Raphael-Boichot/The-TinyGB-Printer/Images/Final_version_2.0_2.png

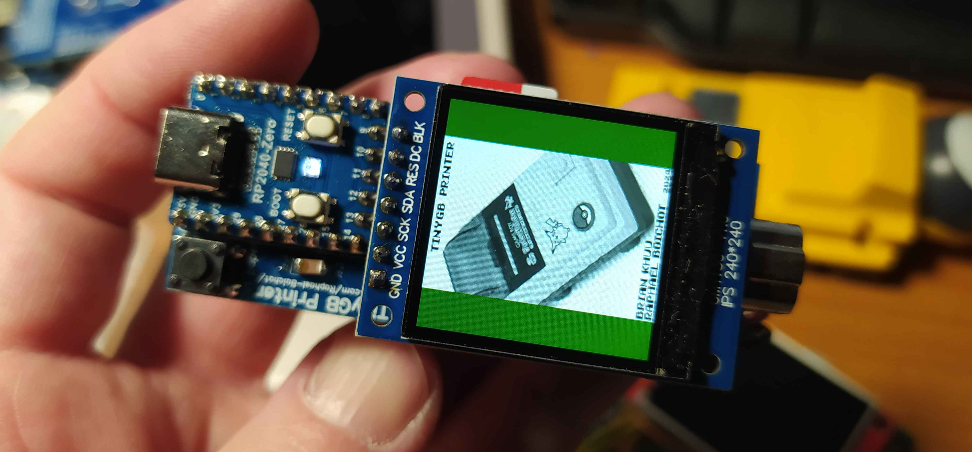
Images/Final_version_2.0_2.png
