Raphael-Boichot/The-TinyGB-Printer/Images/First_prototype.jpg

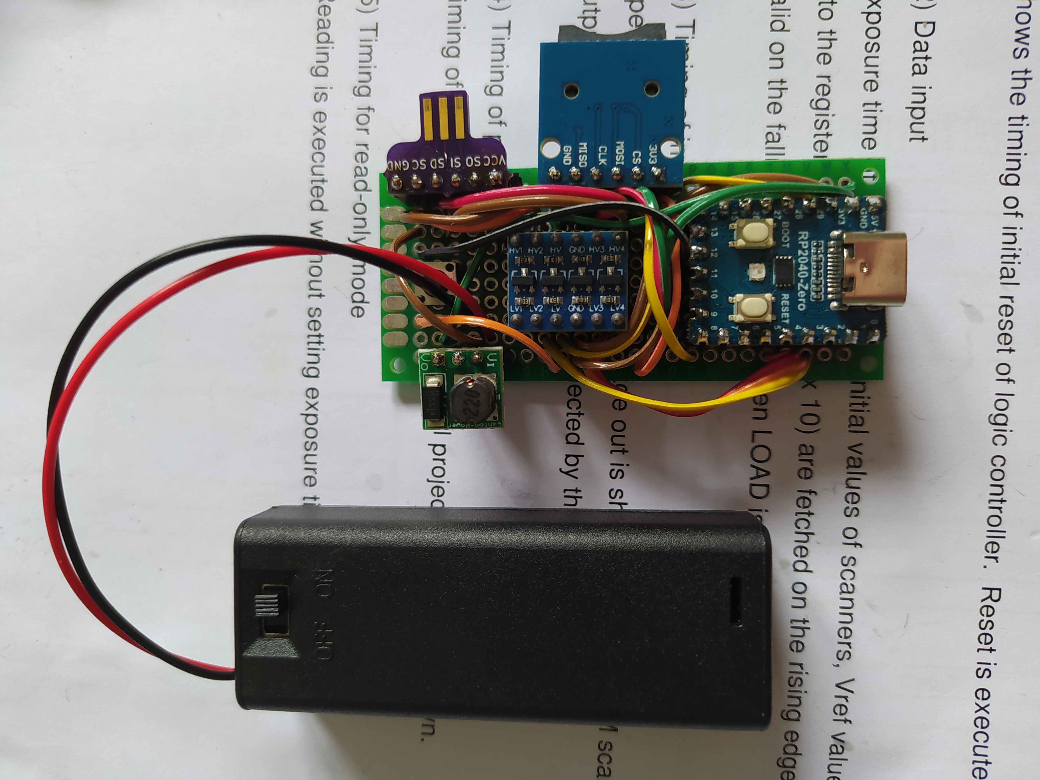
Images/First_prototype.jpg
