Raphael-Boichot/The-TinyGB-Printer/Images/Game_Boy_Camera_2.png

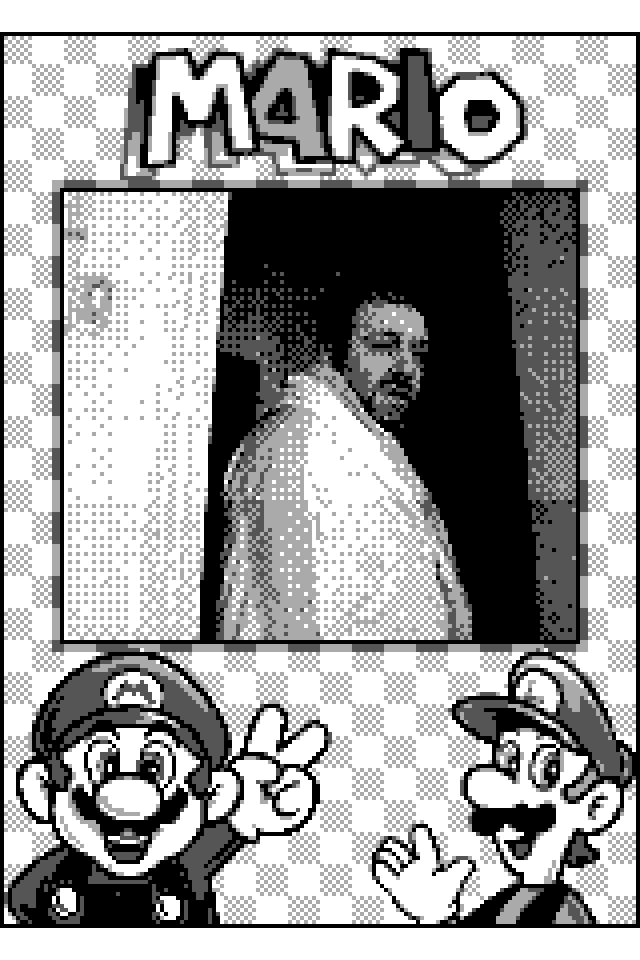
Images/Game_Boy_Camera_2.png
