Raphael-Boichot/The-TinyGB-Printer/Images/Showcase_1.gif

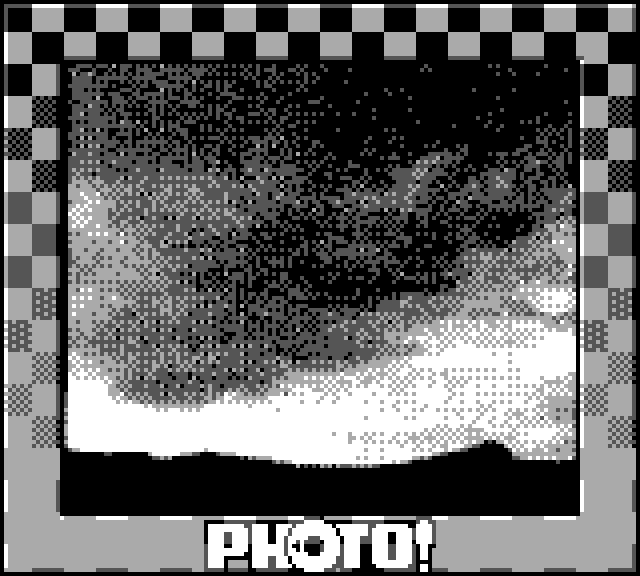
Images/Showcase_1.gif
