Raphael-Boichot/The-TinyGB-Printer/PCB_1.0_without_TFT/PCB.png

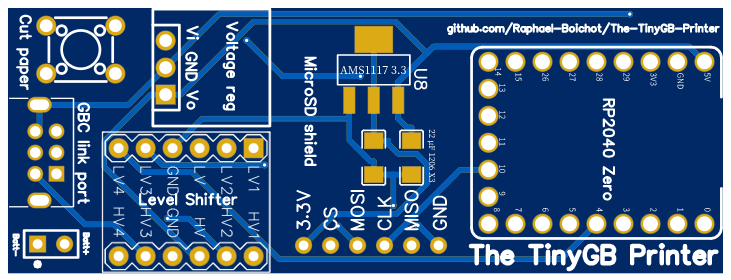
PCB_1.0_without_TFT/PCB.png
