Raphael-Boichot/The-TinyGB-Printer/SD/Script_for_animated_gif/Pictures/0002010.png

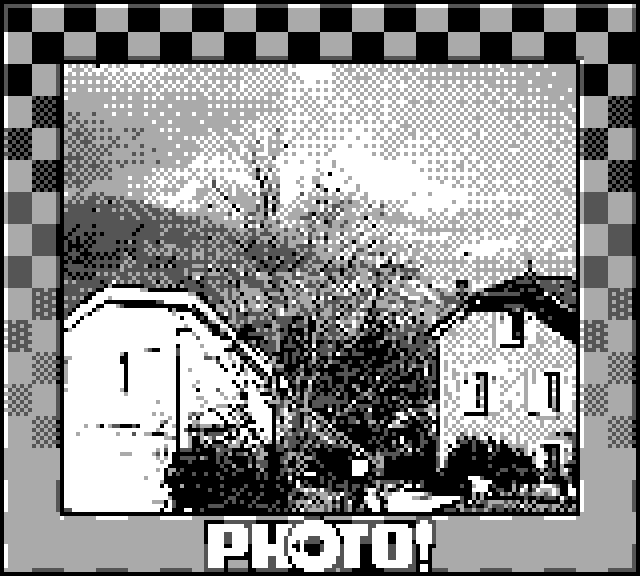
SD/Script_for_animated_gif/Pictures/0002010.png
