Raphael-Boichot/The-TinyGB-Printer/SD/Scripts_for_AEB_mode/Code_black_and_white/Pictures/0004069.png

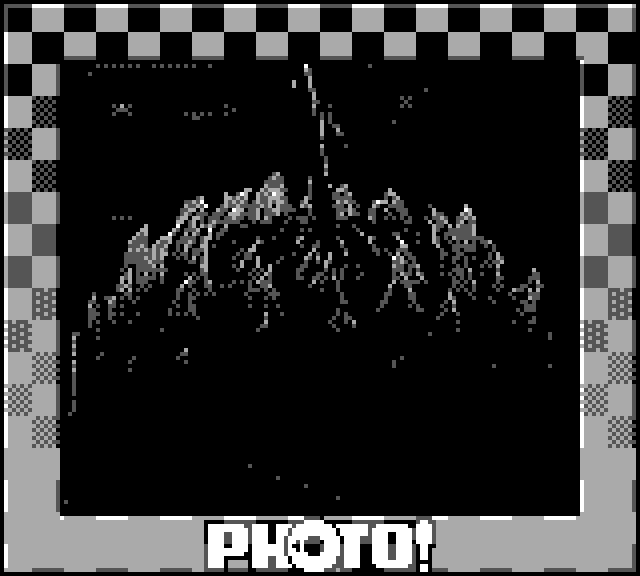
SD/Scripts_for_AEB_mode/Code_black_and_white/Pictures/0004069.png
