Raphael-Boichot/The-TinyGB-Printer/SD/Scripts_for_AEB_mode/Code_color_fusion/Blue_pictures/0004628.png

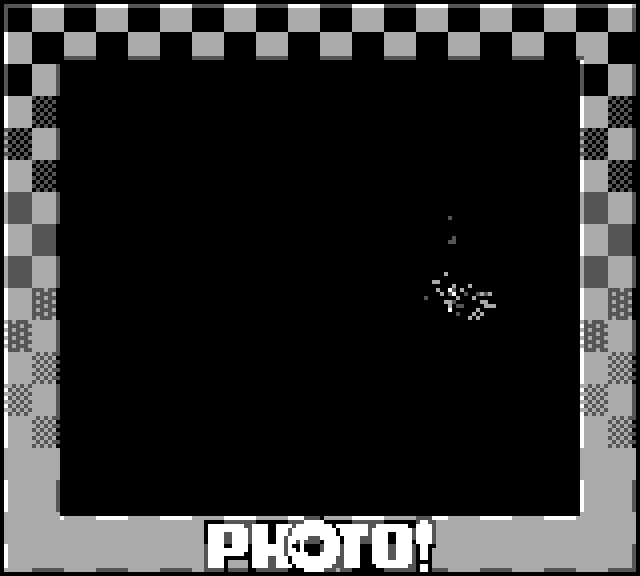
SD/Scripts_for_AEB_mode/Code_color_fusion/Blue_pictures/0004628.png
