Raphael-Boichot/The-TinyGB-Printer/SD/Scripts_for_AEB_mode/Code_color_fusion/Green.png

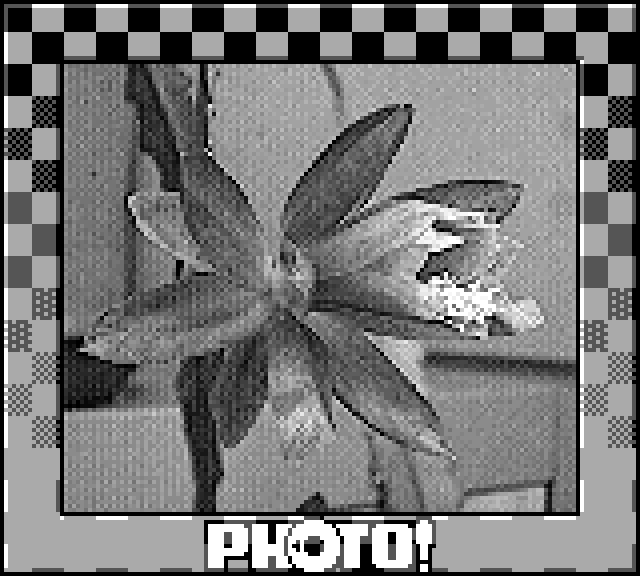
SD/Scripts_for_AEB_mode/Code_color_fusion/Green.png
