Raphael-Boichot/The-TinyGB-Printer/SD/Scripts_for_AEB_mode/Code_color_fusion/Green_pictures/0004589.png

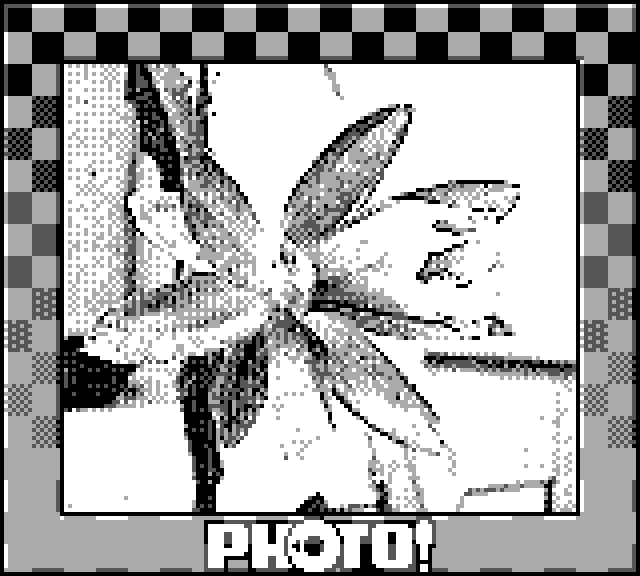
SD/Scripts_for_AEB_mode/Code_color_fusion/Green_pictures/0004589.png
