Raphael-Boichot/The-TinyGB-Printer/SD/Scripts_for_AEB_mode/Code_color_fusion/Red_pictures/0004550.png

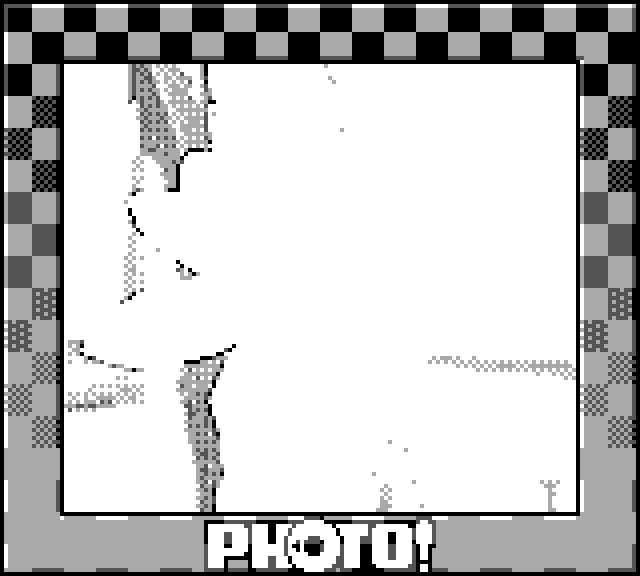
SD/Scripts_for_AEB_mode/Code_color_fusion/Red_pictures/0004550.png
