Raphael-Boichot/The-TinyGB-Printer/SD/Scripts_for_AEB_mode/Examples/Color_fusion_04.png

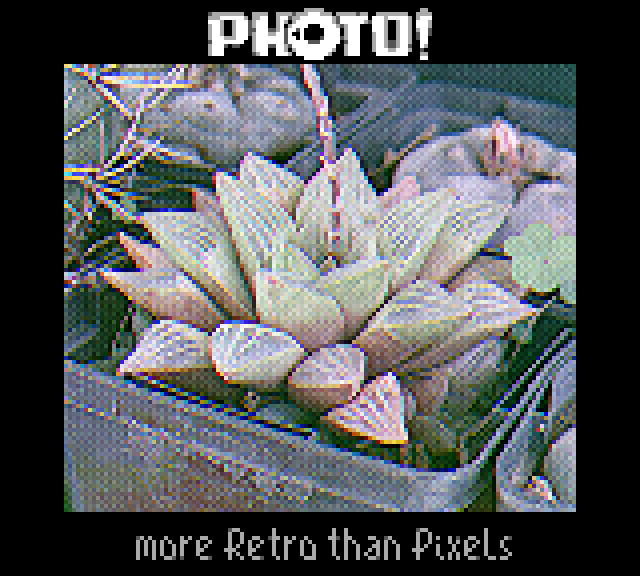
SD/Scripts_for_AEB_mode/Examples/Color_fusion_04.png
