Raphael-Boichot/The-TinyGB-Printer/SD/Scripts_for_AEB_mode/Examples/Color_fusion_05.png

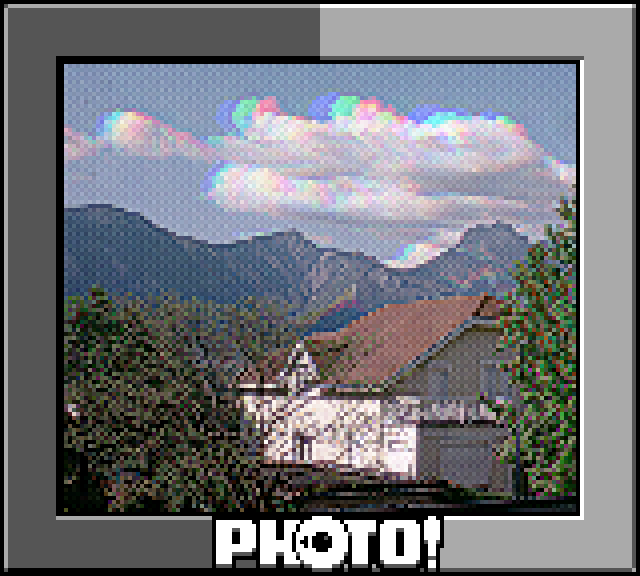
SD/Scripts_for_AEB_mode/Examples/Color_fusion_05.png
