Raphael-Boichot/The-TinyGB-Printer/SD/Scripts_for_AEB_mode/Examples/EAB_image_01.png

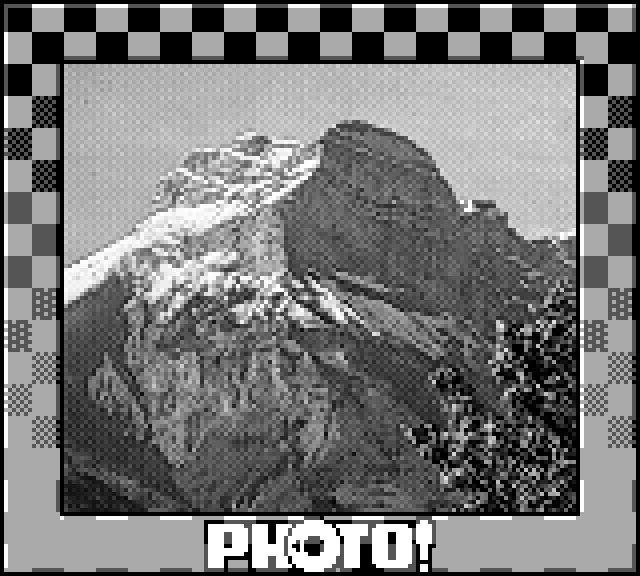
SD/Scripts_for_AEB_mode/Examples/EAB_image_01.png
