Raphael-Boichot/The-TinyGB-Printer/SD/Scripts_for_AEB_mode/Examples/EAB_image_06.png

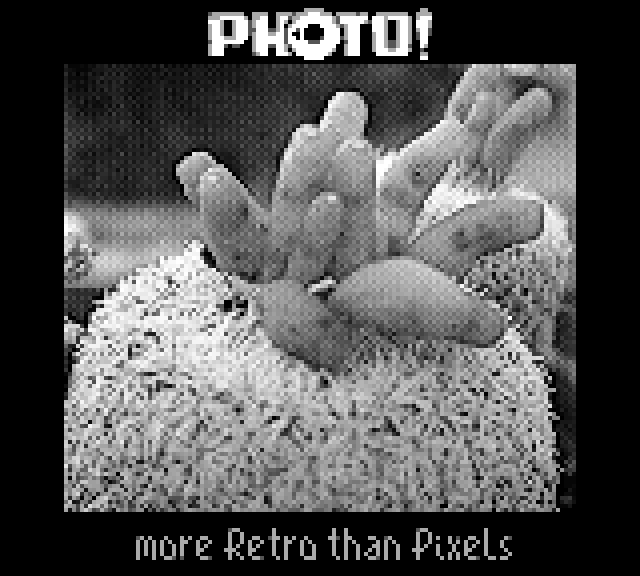
SD/Scripts_for_AEB_mode/Examples/EAB_image_06.png
