Raphael-Boichot/The-TinyGB-Printer/SD/Scripts_for_AEB_mode/Examples/Raw_to_RGB_01.gif

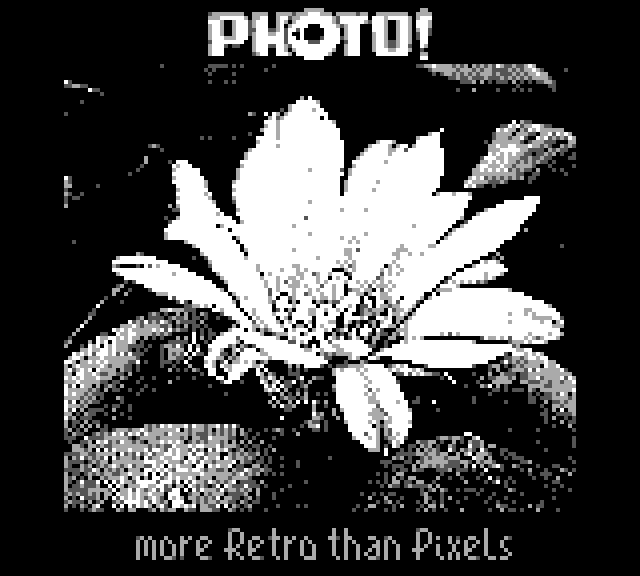
SD/Scripts_for_AEB_mode/Examples/Raw_to_RGB_01.gif
