Raphael-Boichot/The-TinyGB-Printer/TinyGB_Printer/Tools/Fonts.png

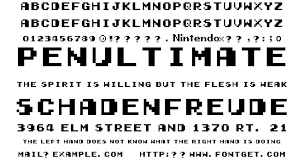
TinyGB_Printer/Tools/Fonts.png
